Patsch91/NerdOCTAXE-Plus/BM1368-1.kicad_sch

## KiCad design BM1368-1.kicad_sch (2024-08-18)

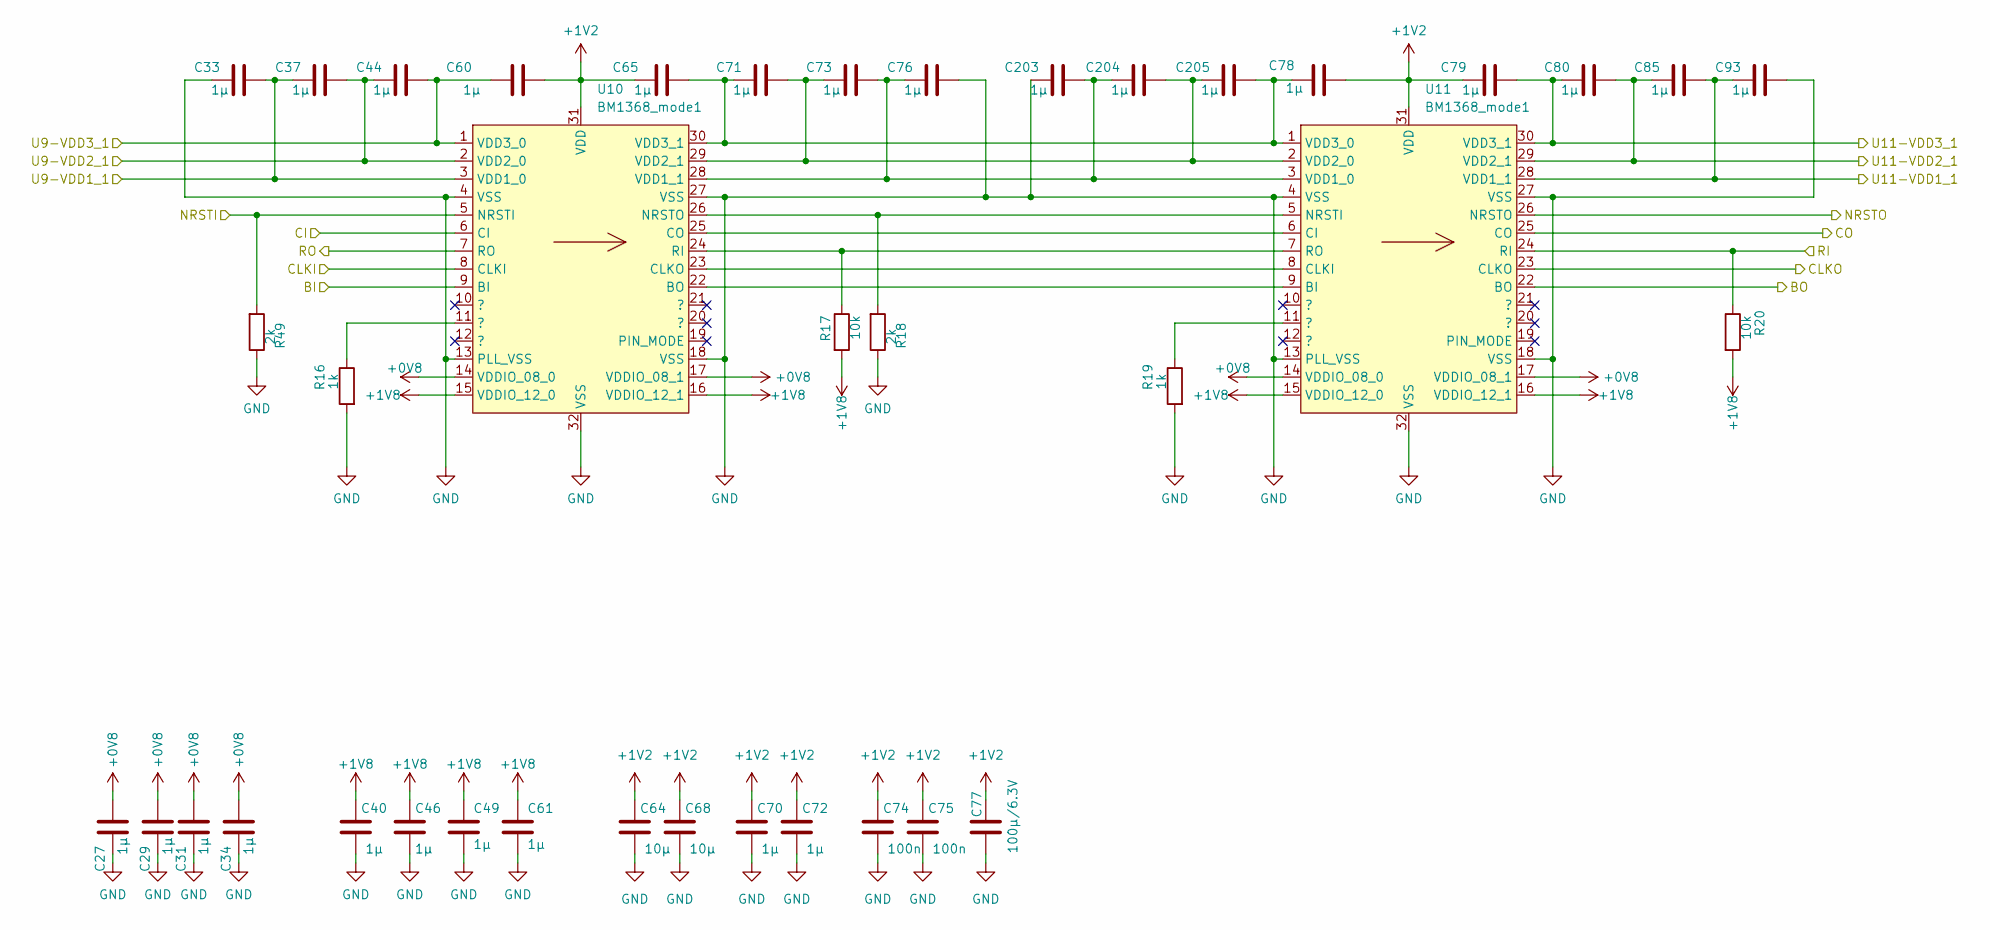
[picture p11: schematic BM1368-1.kicad_sch]

Parts:
C27, C29, C31, C33, C34, C37, C40, C44, C46, C49, C60, C61, C65, C70, C71, C72, C73, C76, C78, C79, C80, C85, C93, C203, C204, C205: 1µ; C_0805_2012Metric
C64, C68: 10µ; C_0805_2012Metric
C74, C75: 100n; C_0805_2012Metric
C77: 100µ/6.3V; C_1210_3225Metric
R16, R19: 1k; R_0805_2012Metric
R17, R20: 10k; R_0805_2012Metric
R18, R49: 2k; R_0805_2012Metric
U10, U11: BM1368_mode1; bm1368-package-modified

Connections:
+0V8: C27.2, C29.2, C31.2, C34.2, U10.14 (VDDIO_08_0), U10.17 (VDDIO_08_1), U11.14 (VDDIO_08_0), U11.17 (VDDIO_08_1)
+1V2: C60.2, C64.1, C65.1, C68.1, C70.1, C72.1, C74.1, C75.1, C77.1, C78.2, C79.1, U10.31 (VDD), U11.31 (VDD)
+1V8: C40.1, C46.1, C49.1, C61.1, R17.2, R20.2, U10.15 (VDDIO_12_0), U10.16 (VDDIO_12_1), U11.15 (VDDIO_12_0), U11.16 (VDDIO_12_1)
BI: U10.9 (BI)
BO: U11.22 (BO)
CI: U10.6 (CI)
CLKI: U10.8 (CLKI)
CLKO: U11.23 (CLKO)
CO: U11.25 (CO)
GND: C27.1, C29.1, C31.1, C33.1, C34.1, C40.2, C46.2, C49.2, C61.2, C64.2, C68.2, C70.2, C72.2, C74.2, C75.2, C76.2, C77.2, C93.2, C203.1, R16.2, R18.1, R19.2, R49.1, U10.4 (VSS), U10.13 (PLL_VSS), U10.18 (VSS), U10.27 (VSS), U10.32 (VSS), U11.4 (VSS), U11.13 (PLL_VSS), U11.18 (VSS), U11.27 (VSS), U11.32 (VSS)
NRSTI: R49.2, U10.5 (NRSTI)
NRSTO: U11.26 (NRSTO)
unnamed: C73.2, C76.1, C203.2, C204.1, U10.28 (VDD1_1), U11.3 (VDD1_0)
unnamed: C71.2, C73.1, C204.2, C205.1, U10.29 (VDD2_1), U11.2 (VDD2_0)
unnamed: C65.2, C71.1, C78.1, C205.2, U10.30 (VDD3_1), U11.1 (VDD3_0)
unnamed: R16.1, U10.11 (?)
unnamed: R17.1, U10.24 (RI), U11.7 (RO)
unnamed: R18.2, U10.26 (NRSTO), U11.5 (NRSTI)
unnamed: R19.1, U11.11 (?)
unnamed: U10.22 (BO), U11.9 (BI)
unnamed: U10.23 (CLKO), U11.8 (CLKI)
unnamed: U10.25 (CO), U11.6 (CI)
RI: R20.1, U11.24 (RI)
RO: U10.7 (RO)
U9-VDD1_1: C33.2, C37.1, U10.3 (VDD1_0)
U9-VDD2_1: C37.2, C44.1, U10.2 (VDD2_0)
U9-VDD3_1: C44.2, C60.1, U10.1 (VDD3_0)
U11-VDD1_1: C85.2, C93.1, U11.28 (VDD1_1)
U11-VDD2_1: C80.2, C85.1, U11.29 (VDD2_1)
U11-VDD3_1: C79.2, C80.1, U11.30 (VDD3_1)
