Patsch91/NerdOCTAXE-Plus/BM1368-2.kicad_sch

## KiCad design BM1368-2.kicad_sch (2024-08-18)

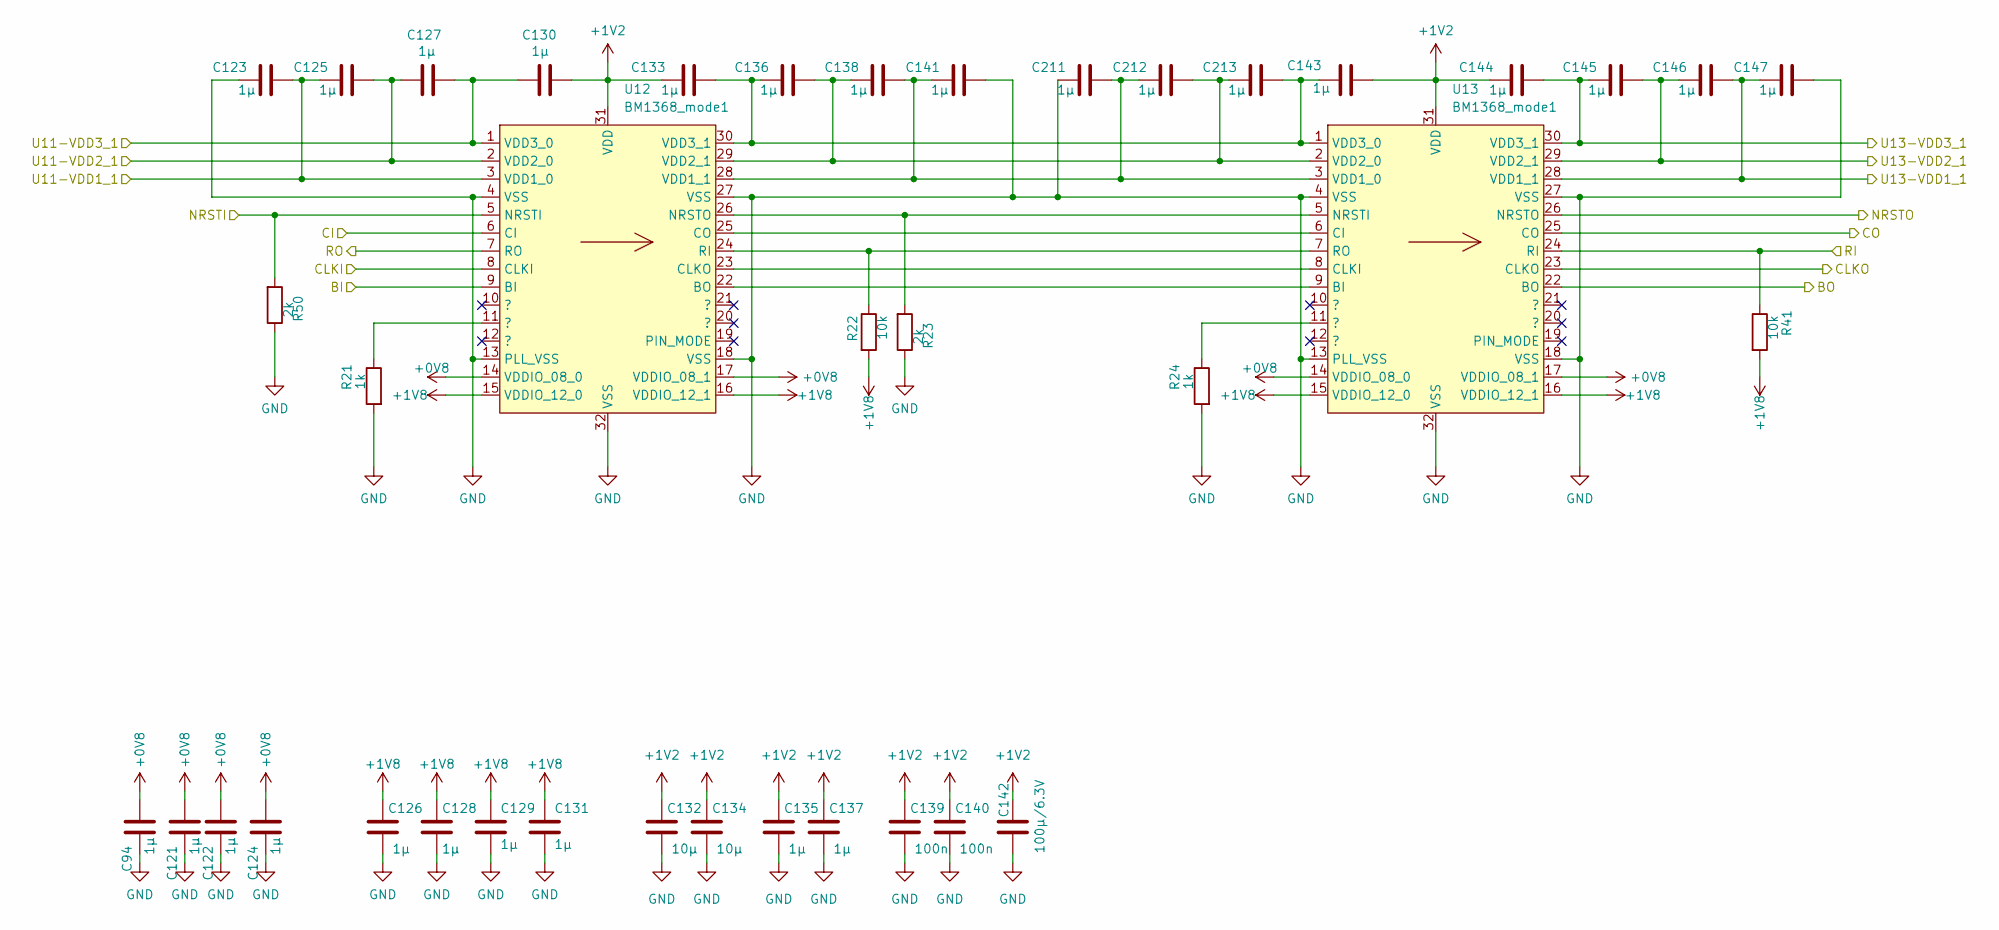
[picture p12: schematic BM1368-2.kicad_sch]

Parts:
C94, C121, C122, C123, C124, C125, C126, C127, C128, C129, C130, C131, C133, C135, C136, C137, C138, C141, C143, C144, C145, C146, C147, C211, C212, C213: 1µ; C_0805_2012Metric
C132, C134: 10µ; C_0805_2012Metric
C139, C140: 100n; C_0805_2012Metric
C142: 100µ/6.3V; C_1210_3225Metric
R21, R24: 1k; R_0805_2012Metric
R22, R41: 10k; R_0805_2012Metric
R23, R50: 2k; R_0805_2012Metric
U12, U13: BM1368_mode1; bm1368-package-modified

Connections:
+0V8: C94.2, C121.2, C122.2, C124.2, U12.14 (VDDIO_08_0), U12.17 (VDDIO_08_1), U13.14 (VDDIO_08_0), U13.17 (VDDIO_08_1)
+1V2: C130.2, C132.1, C133.1, C134.1, C135.1, C137.1, C139.1, C140.1, C142.1, C143.2, C144.1, U12.31 (VDD), U13.31 (VDD)
+1V8: C126.1, C128.1, C129.1, C131.1, R22.2, R41.2, U12.15 (VDDIO_12_0), U12.16 (VDDIO_12_1), U13.15 (VDDIO_12_0), U13.16 (VDDIO_12_1)
BI: U12.9 (BI)
BO: U13.22 (BO)
CI: U12.6 (CI)
CLKI: U12.8 (CLKI)
CLKO: U13.23 (CLKO)
CO: U13.25 (CO)
GND: C94.1, C121.1, C122.1, C123.1, C124.1, C126.2, C128.2, C129.2, C131.2, C132.2, C134.2, C135.2, C137.2, C139.2, C140.2, C141.2, C142.2, C147.2, C211.1, R21.2, R23.1, R24.2, R50.1, U12.4 (VSS), U12.13 (PLL_VSS), U12.18 (VSS), U12.27 (VSS), U12.32 (VSS), U13.4 (VSS), U13.13 (PLL_VSS), U13.18 (VSS), U13.27 (VSS), U13.32 (VSS)
NRSTI: R50.2, U12.5 (NRSTI)
NRSTO: U13.26 (NRSTO)
unnamed: C133.2, C136.1, C143.1, C213.2, U12.30 (VDD3_1), U13.1 (VDD3_0)
unnamed: C136.2, C138.1, C212.2, C213.1, U12.29 (VDD2_1), U13.2 (VDD2_0)
unnamed: C138.2, C141.1, C211.2, C212.1, U12.28 (VDD1_1), U13.3 (VDD1_0)
unnamed: R21.1, U12.11 (?)
unnamed: R22.1, U12.24 (RI), U13.7 (RO)
unnamed: R23.2, U12.26 (NRSTO), U13.5 (NRSTI)
unnamed: R24.1, U13.11 (?)
unnamed: U12.22 (BO), U13.9 (BI)
unnamed: U12.23 (CLKO), U13.8 (CLKI)
unnamed: U12.25 (CO), U13.6 (CI)
RI: R41.1, U13.24 (RI)
RO: U12.7 (RO)
U11-VDD1_1: C123.2, C125.1, U12.3 (VDD1_0)
U11-VDD2_1: C125.2, C127.1, U12.2 (VDD2_0)
U11-VDD3_1: C127.2, C130.1, U12.1 (VDD3_0)
U13-VDD1_1: C146.2, C147.1, U13.28 (VDD1_1)
U13-VDD2_1: C145.2, C146.1, U13.29 (VDD2_1)
U13-VDD3_1: C144.2, C145.1, U13.30 (VDD3_1)
