Patsch91/NerdOCTAXE-Plus/BM1368-3.kicad_sch

## KiCad design BM1368-3.kicad_sch (2024-08-18)

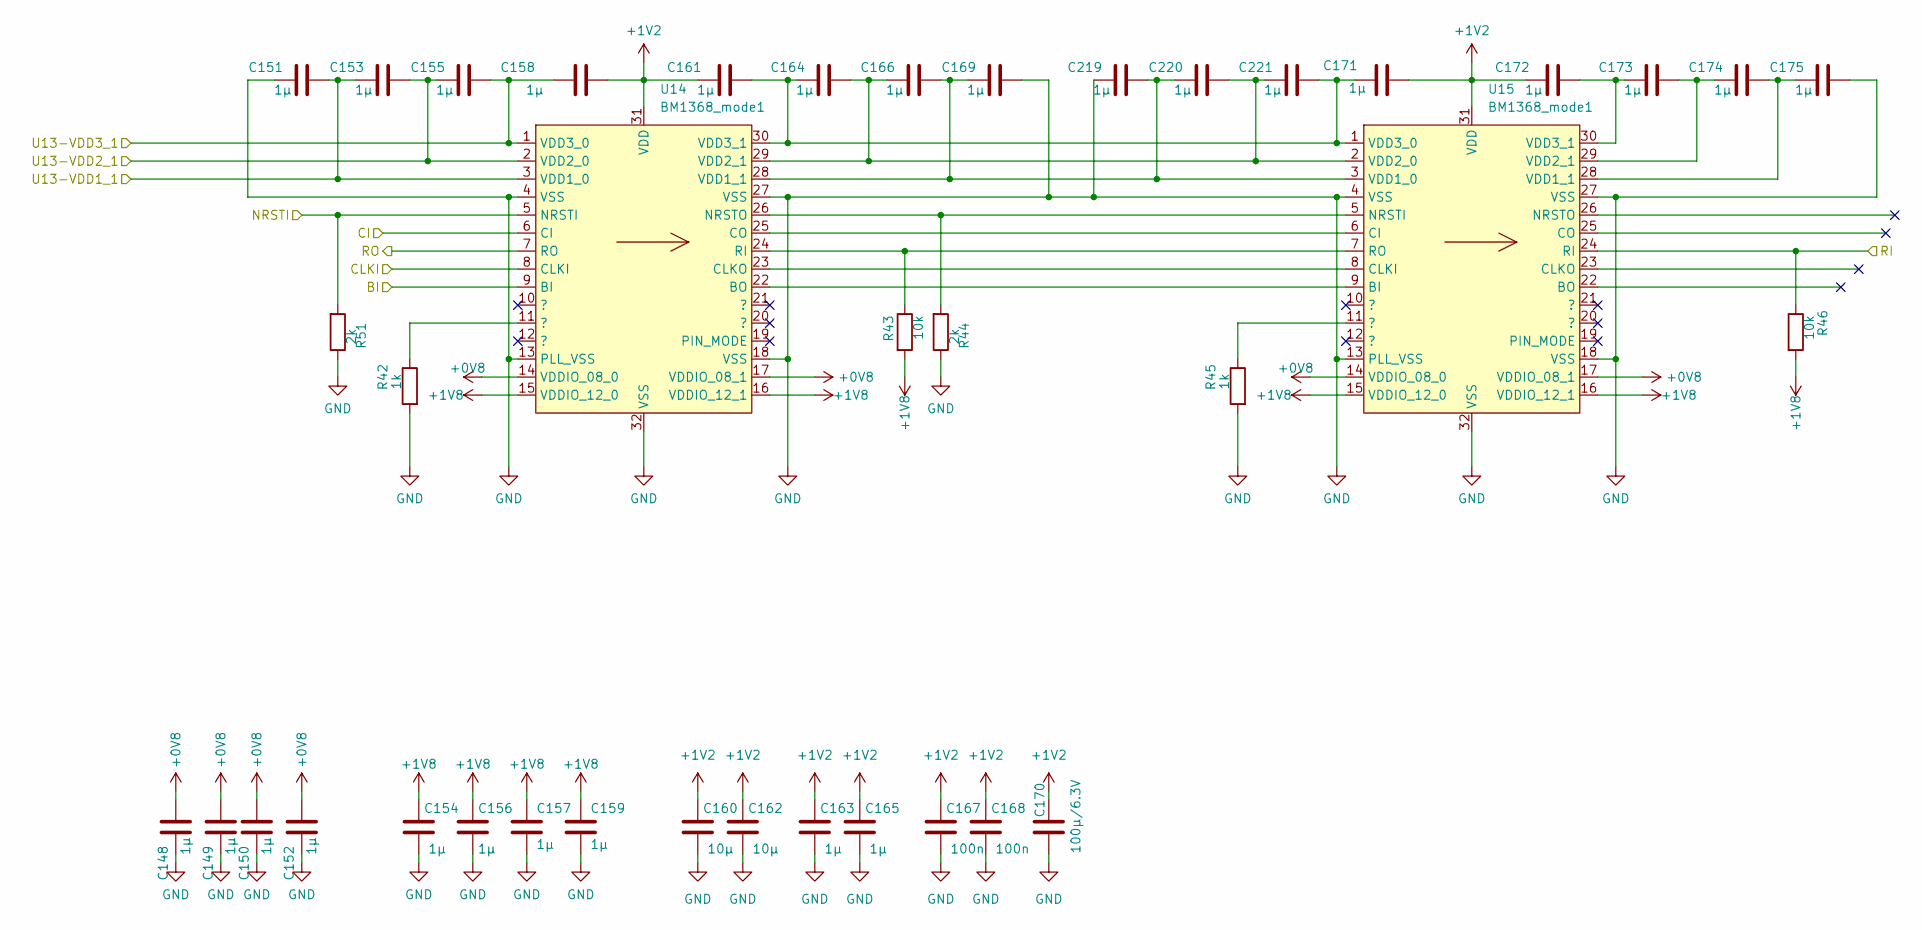
[picture p13: schematic BM1368-3.kicad_sch]

Parts:
C148, C149, C150, C151, C152, C153, C154, C155, C156, C157, C158, C159, C161, C163, C164, C165, C166, C169, C171, C172, C173, C174, C175, C219, C220, C221: 1µ; C_0805_2012Metric
C160, C162: 10µ; C_0805_2012Metric
C167, C168: 100n; C_0805_2012Metric
C170: 100µ/6.3V; C_1210_3225Metric
R42, R45: 1k; R_0805_2012Metric
R43, R46: 10k; R_0805_2012Metric
R44, R51: 2k; R_0805_2012Metric
U14, U15: BM1368_mode1; bm1368-package-modified

Connections:
+0V8: C148.2, C149.2, C150.2, C152.2, U14.14 (VDDIO_08_0), U14.17 (VDDIO_08_1), U15.14 (VDDIO_08_0), U15.17 (VDDIO_08_1)
+1V2: C158.2, C160.1, C161.1, C162.1, C163.1, C165.1, C167.1, C168.1, C170.1, C171.2, C172.1, U14.31 (VDD), U15.31 (VDD)
+1V8: C154.1, C156.1, C157.1, C159.1, R43.2, R46.2, U14.15 (VDDIO_12_0), U14.16 (VDDIO_12_1), U15.15 (VDDIO_12_0), U15.16 (VDDIO_12_1)
BI: U14.9 (BI)
CI: U14.6 (CI)
CLKI: U14.8 (CLKI)
GND: C148.1, C149.1, C150.1, C151.1, C152.1, C154.2, C156.2, C157.2, C159.2, C160.2, C162.2, C163.2, C165.2, C167.2, C168.2, C169.2, C170.2, C175.2, C219.1, R42.2, R44.1, R45.2, R51.1, U14.4 (VSS), U14.13 (PLL_VSS), U14.18 (VSS), U14.27 (VSS), U14.32 (VSS), U15.4 (VSS), U15.13 (PLL_VSS), U15.18 (VSS), U15.27 (VSS), U15.32 (VSS)
NRSTI: R51.2, U14.5 (NRSTI)
unnamed: C161.2, C164.1, C171.1, C221.2, U14.30 (VDD3_1), U15.1 (VDD3_0)
unnamed: C164.2, C166.1, C220.2, C221.1, U14.29 (VDD2_1), U15.2 (VDD2_0)
unnamed: C166.2, C169.1, C219.2, C220.1, U14.28 (VDD1_1), U15.3 (VDD1_0)
unnamed: C172.2, C173.1, U15.30 (VDD3_1)
unnamed: C173.2, C174.1, U15.29 (VDD2_1)
unnamed: C174.2, C175.1, U15.28 (VDD1_1)
unnamed: R42.1, U14.11 (?)
unnamed: R43.1, U14.24 (RI), U15.7 (RO)
unnamed: R44.2, U14.26 (NRSTO), U15.5 (NRSTI)
unnamed: R45.1, U15.11 (?)
unnamed: U14.22 (BO), U15.9 (BI)
unnamed: U14.23 (CLKO), U15.8 (CLKI)
unnamed: U14.25 (CO), U15.6 (CI)
RI: R46.1, U15.24 (RI)
RO: U14.7 (RO)
U13-VDD1_1: C151.2, C153.1, U14.3 (VDD1_0)
U13-VDD2_1: C153.2, C155.1, U14.2 (VDD2_0)
U13-VDD3_1: C155.2, C158.1, U14.1 (VDD3_0)
