Patsch91/NerdOCTAXE-Plus/BM1368.kicad_sch

## KiCad design BM1368.kicad_sch (2024-08-18)

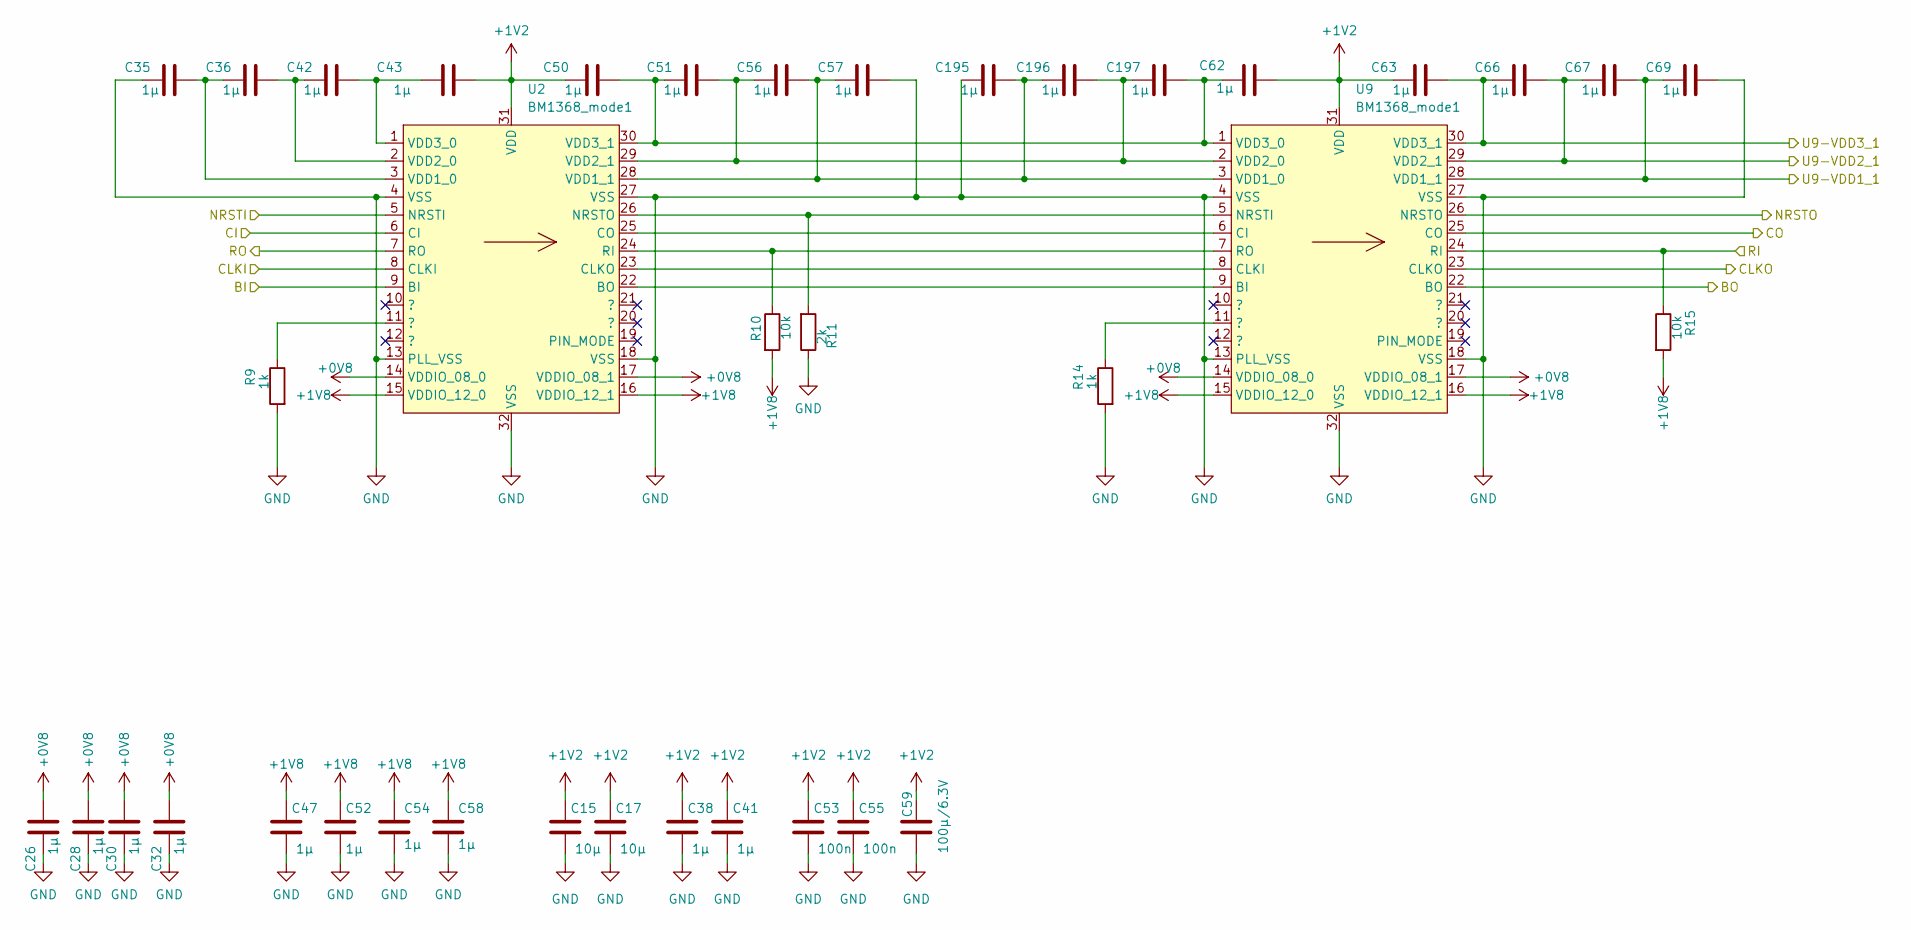
[picture p14: schematic BM1368.kicad_sch]

Parts:
C15, C17: 10µ; C_0805_2012Metric
C26, C28, C30, C32, C35, C36, C38, C41, C42, C43, C47, C50, C51, C52, C54, C56, C57, C58, C62, C63, C66, C67, C69, C195, C196, C197: 1µ; C_0805_2012Metric
C53, C55: 100n; C_0805_2012Metric
C59: 100µ/6.3V; C_1210_3225Metric
R9, R14: 1k; R_0805_2012Metric
R10, R15: 10k; R_0805_2012Metric
R11: 2k; R_0805_2012Metric
U2, U9: BM1368_mode1; bm1368-package-modified

Connections:
+0V8: C26.2, C28.2, C30.2, C32.2, U2.14 (VDDIO_08_0), U2.17 (VDDIO_08_1), U9.14 (VDDIO_08_0), U9.17 (VDDIO_08_1)
+1V2: C15.1, C17.1, C38.1, C41.1, C43.2, C50.1, C53.1, C55.1, C59.1, C62.2, C63.1, U2.31 (VDD), U9.31 (VDD)
+1V8: C47.1, C52.1, C54.1, C58.1, R10.2, R15.2, U2.15 (VDDIO_12_0), U2.16 (VDDIO_12_1), U9.15 (VDDIO_12_0), U9.16 (VDDIO_12_1)
BI: U2.9 (BI)
BO: U9.22 (BO)
CI: U2.6 (CI)
CLKI: U2.8 (CLKI)
CLKO: U9.23 (CLKO)
CO: U9.25 (CO)
GND: C15.2, C17.2, C26.1, C28.1, C30.1, C32.1, C35.1, C38.2, C41.2, C47.2, C52.2, C53.2, C54.2, C55.2, C57.2, C58.2, C59.2, C69.2, C195.1, R9.2, R11.1, R14.2, U2.4 (VSS), U2.13 (PLL_VSS), U2.18 (VSS), U2.27 (VSS), U2.32 (VSS), U9.4 (VSS), U9.13 (PLL_VSS), U9.18 (VSS), U9.27 (VSS), U9.32 (VSS)
NRSTI: U2.5 (NRSTI)
NRSTO: U9.26 (NRSTO)
unnamed: C35.2, C36.1, U2.3 (VDD1_0)
unnamed: C36.2, C42.1, U2.2 (VDD2_0)
unnamed: C42.2, C43.1, U2.1 (VDD3_0)
unnamed: C56.2, C57.1, C195.2, C196.1, U2.28 (VDD1_1), U9.3 (VDD1_0)
unnamed: C51.2, C56.1, C196.2, C197.1, U2.29 (VDD2_1), U9.2 (VDD2_0)
unnamed: C50.2, C51.1, C62.1, C197.2, U2.30 (VDD3_1), U9.1 (VDD3_0)
unnamed: R9.1, U2.11 (?)
unnamed: R10.1, U2.24 (RI), U9.7 (RO)
unnamed: R11.2, U2.26 (NRSTO), U9.5 (NRSTI)
unnamed: R14.1, U9.11 (?)
unnamed: U2.22 (BO), U9.9 (BI)
unnamed: U2.23 (CLKO), U9.8 (CLKI)
unnamed: U2.25 (CO), U9.6 (CI)
RI: R15.1, U9.24 (RI)
RO: U2.7 (RO)
U9-VDD1_1: C67.2, C69.1, U9.28 (VDD1_1)
U9-VDD2_1: C66.2, C67.1, U9.29 (VDD2_1)
U9-VDD3_1: C63.2, C66.1, U9.30 (VDD3_1)
