Patsch91/NerdOCTAXE-Plus/Nerd8.kicad_sch

## KiCad design Nerd8.kicad_sch (2024-09-09)

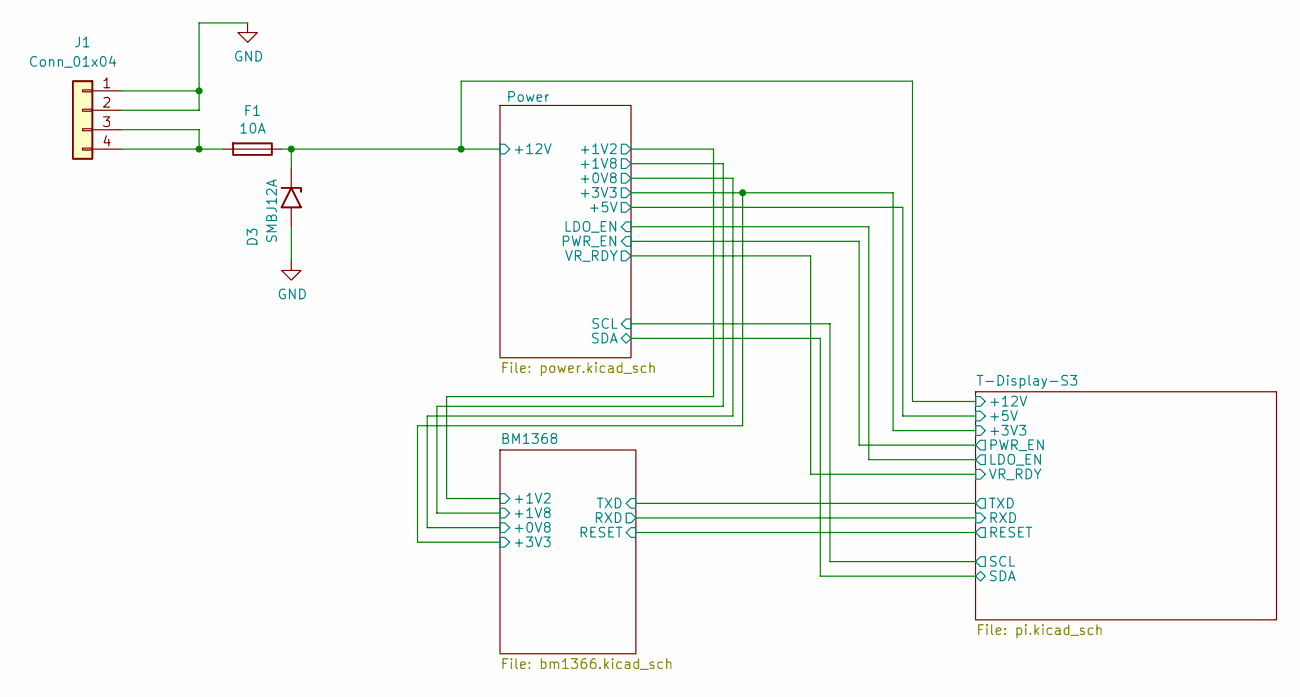
[picture p15: schematic Nerd8.kicad_sch]

Parts:
D3: SMBJ12A; D_SMB
F1: 10A; fuseholder_littlefuse_blok
J1: Conn_01x04; Barrier Terminal 01x04

Connections:
+12V: D3.1 (A1), F1.1
GND: D3.2 (A2), J1.1, J1.2
unnamed: F1.2, J1.3, J1.4
