Patsch91/NerdOCTAXE-Plus/bm1366.kicad_sch

## KiCad design bm1366.kicad_sch (2024-08-18)

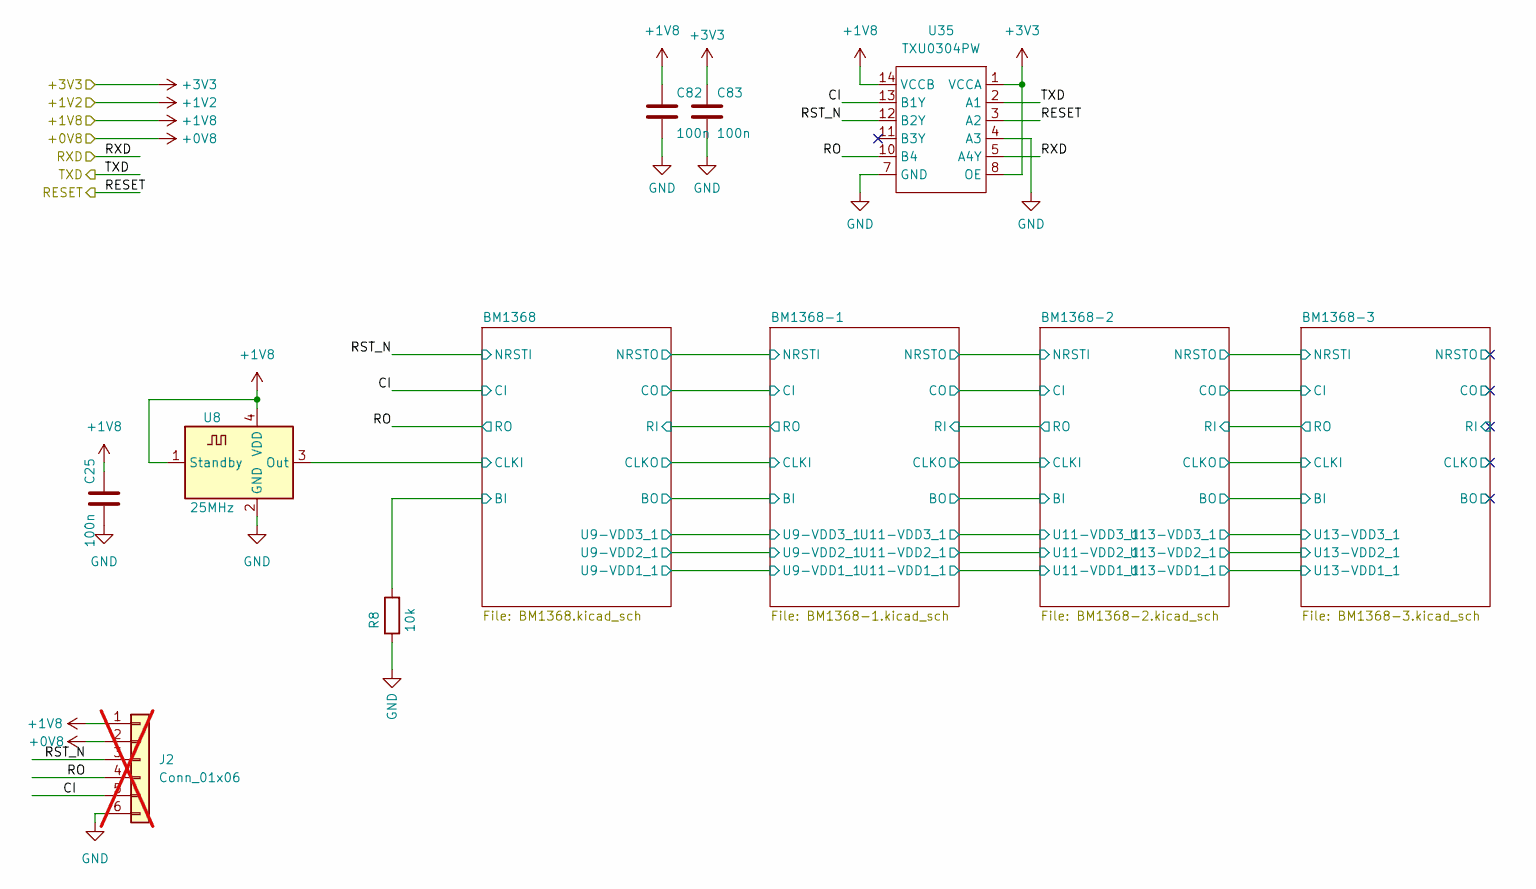
[picture p16: schematic bm1366.kicad_sch]

Parts:
C25, C82, C83: 100n; C_0805_2012Metric
J2: Conn_01x06; PinHeader_1x06_P1.27mm_Vertical; not fitted
R8: 10k; R_0805_2012Metric
U8: 25MHz; Oscillator_SMD_EuroQuartz_XO32-4Pin_3.2x2.5mm
U35: TXU0304PW; TSSOP-14-1EP_4.4x5mm_P0.65mm

Connections:
+0V8: J2.2
+1V8: C25.1, C82.1, J2.1, U8.1 (Standby), U8.4 (VDD), U35.14 (VCCB)
+3V3: C83.1, U35.1 (VCCA), U35.8 (OE)
BI: R8.2
CI: J2.5, U35.13 (B1Y)
CLKI: U8.3 (Out)
GND: C25.2, C82.2, C83.2, J2.6, R8.1, U8.2 (GND), U35.4 (A3), U35.7 (GND)
RESET: U35.3 (A2)
RO: J2.4, U35.10 (B4)
RST_N: J2.3, U35.12 (B2Y)
RXD: U35.5 (A4Y)
TXD: U35.2 (A1)
