Patsch91/NerdOCTAXE-Plus/pi.kicad_sch

## KiCad design pi.kicad_sch (2024-08-14)

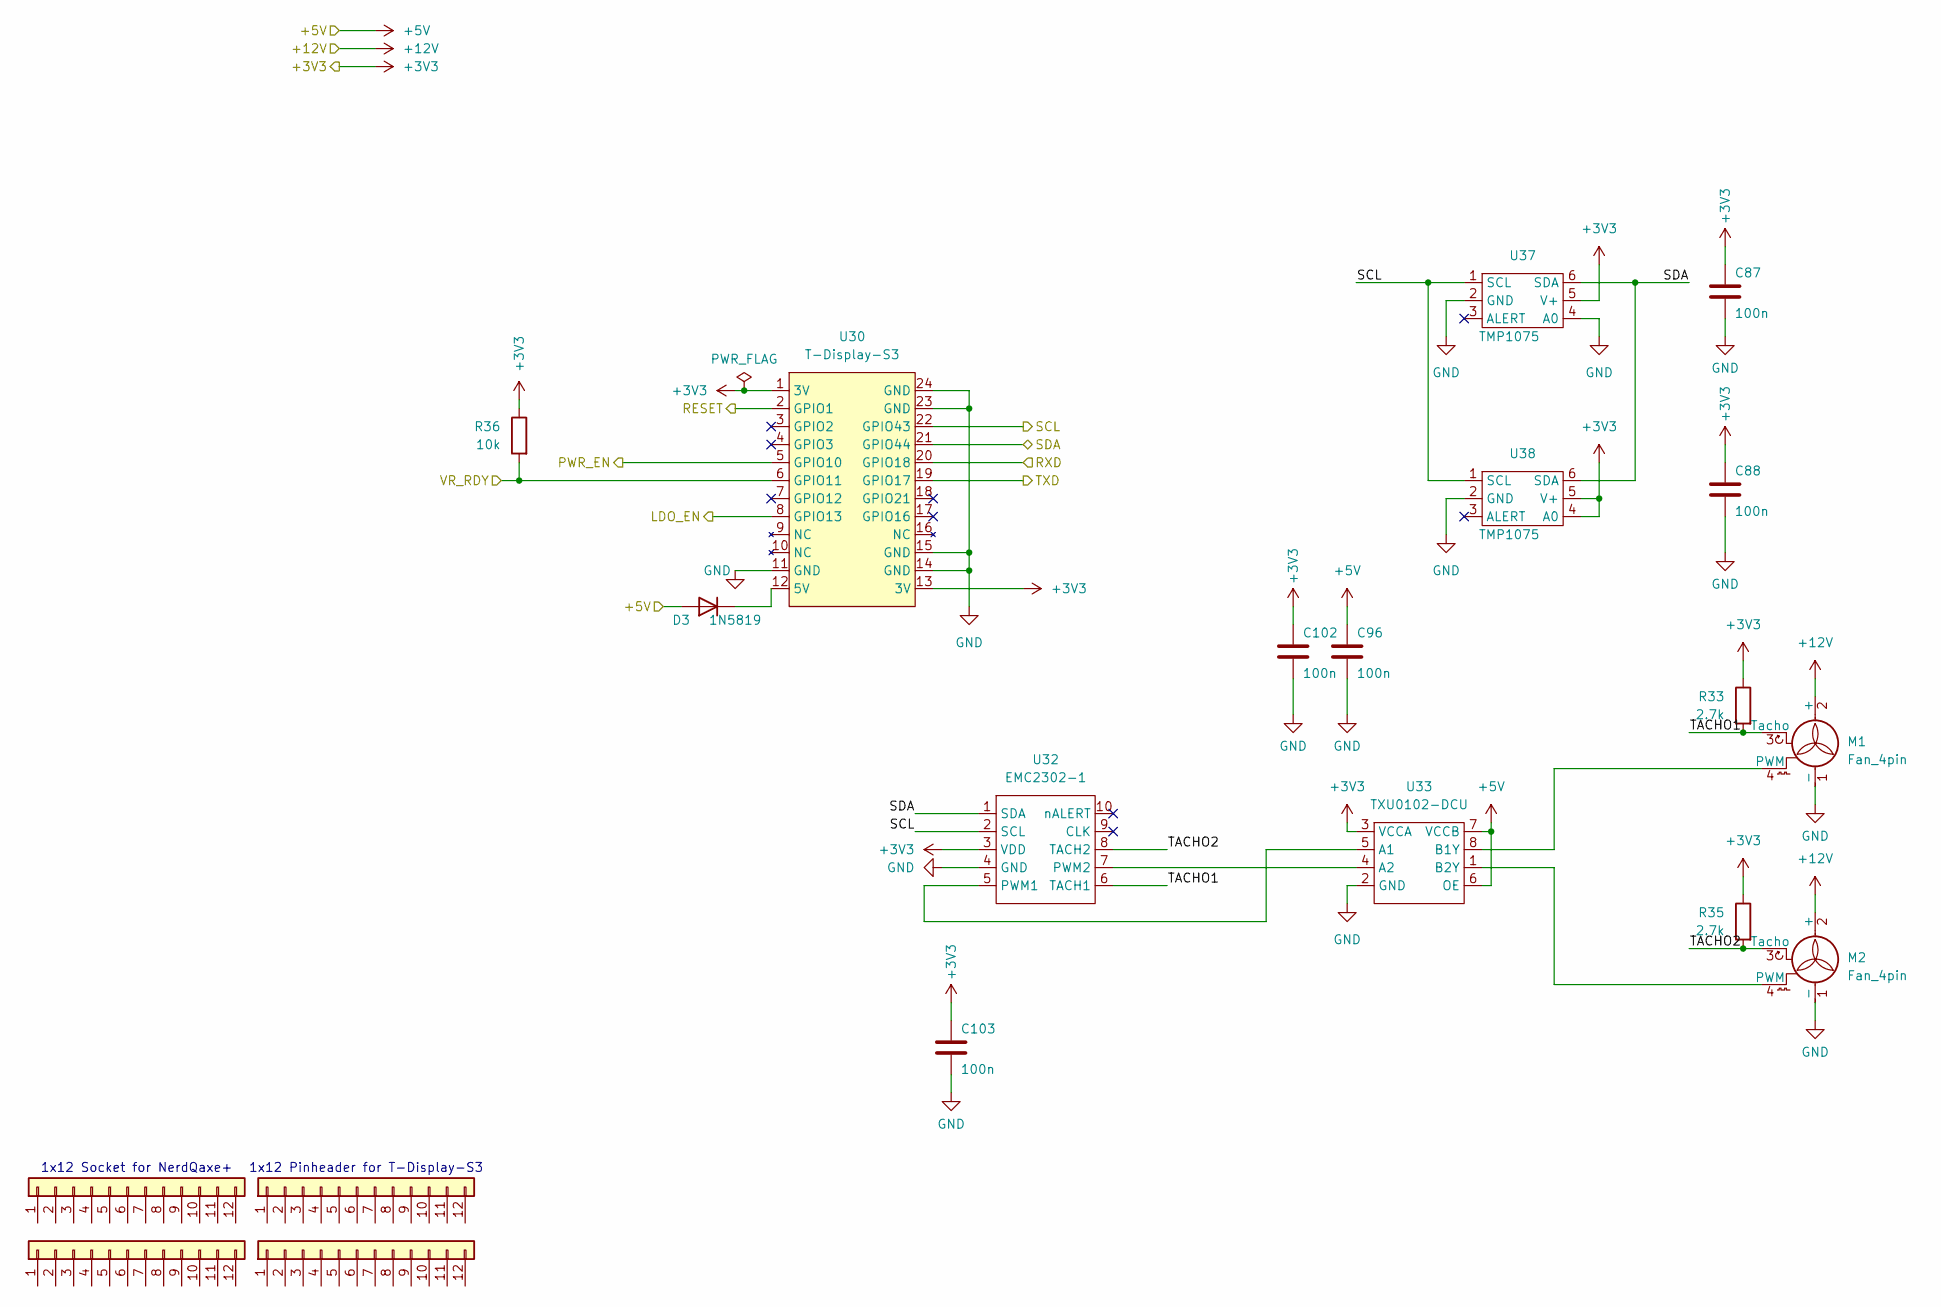
[picture p17: schematic pi.kicad_sch]

Parts:
C87, C88, C96, C102, C103: 100n; C_0805_2012Metric
D3: 1N5819; D_SOD-123
J5, J6: Conn_01x12-Socket
J7, J8: Conn_01x12-Header
M1, M2: Fan_4pin; FanPinHeader_1x04_P2.54mm_Vertical
R33, R35: 2.7k; R_0805_2012Metric
R36: 10k; R_0805_2012Metric
U30: T-Display-S3
U32: EMC2302-1; MSOP-10_3x3mm_P0.5mm
U33: TXU0102-DCU; VSSOP-8_2.3x2mm_P0.5mm
U37, U38: TMP1075; TMP1075-DRL

Connections:
+3V3: C87.1, C88.1, C102.1, C103.1, R33.1, R35.1, R36.1, U30.1 (3V), U30.13 (3V), U32.3 (VDD), U33.3 (VCCA), U37.5 (V+), U38.4 (A0), U38.5 (V+)
+5V: C96.1, D3.2 (A), U33.6 (OE), U33.7 (VCCB)
+12V: M1.2 (+), M2.2 (+)
GND: C87.2, C88.2, C96.2, C102.2, C103.2, M1.1 (-), M2.1 (-), U30.11 (GND), U30.14 (GND), U30.15 (GND), U30.23 (GND), U30.24 (GND), U32.4 (GND), U33.2 (GND), U37.2 (GND), U37.4 (A0), U38.2 (GND)
LDO_EN: U30.8 (GPIO13)
unnamed: D3.1 (K), U30.12 (5V)
unnamed: M1.4 (PWM), U33.8 (B1Y)
unnamed: M2.4 (PWM), U33.1 (B2Y)
unnamed: U32.5 (PWM1), U33.5 (A1)
unnamed: U32.7 (PWM2), U33.4 (A2)
PWR_EN: U30.5 (GPIO10)
RESET: U30.2 (GPIO1)
RXD: U30.20 (GPIO18)
SCL: U30.22 (GPIO43), U32.2 (SCL), U37.1 (SCL), U38.1 (SCL)
SDA: U30.21 (GPIO44), U32.1 (SDA), U37.6 (SDA), U38.6 (SDA)
TACHO1: M1.3 (Tacho), R33.2, U32.6 (TACH1)
TACHO2: M2.3 (Tacho), R35.2, U32.8 (TACH2)
TXD: U30.19 (GPIO17)
VR_RDY: R36.2, U30.6 (GPIO11)

Notes on the sheet:
1x12 Socket for NerdQaxe+
1x12 Pinheader for T-Display-S3
