Patsch91/NerdOCTAXE-Plus/power.kicad_sch

## KiCad design power.kicad_sch (2024-09-18)

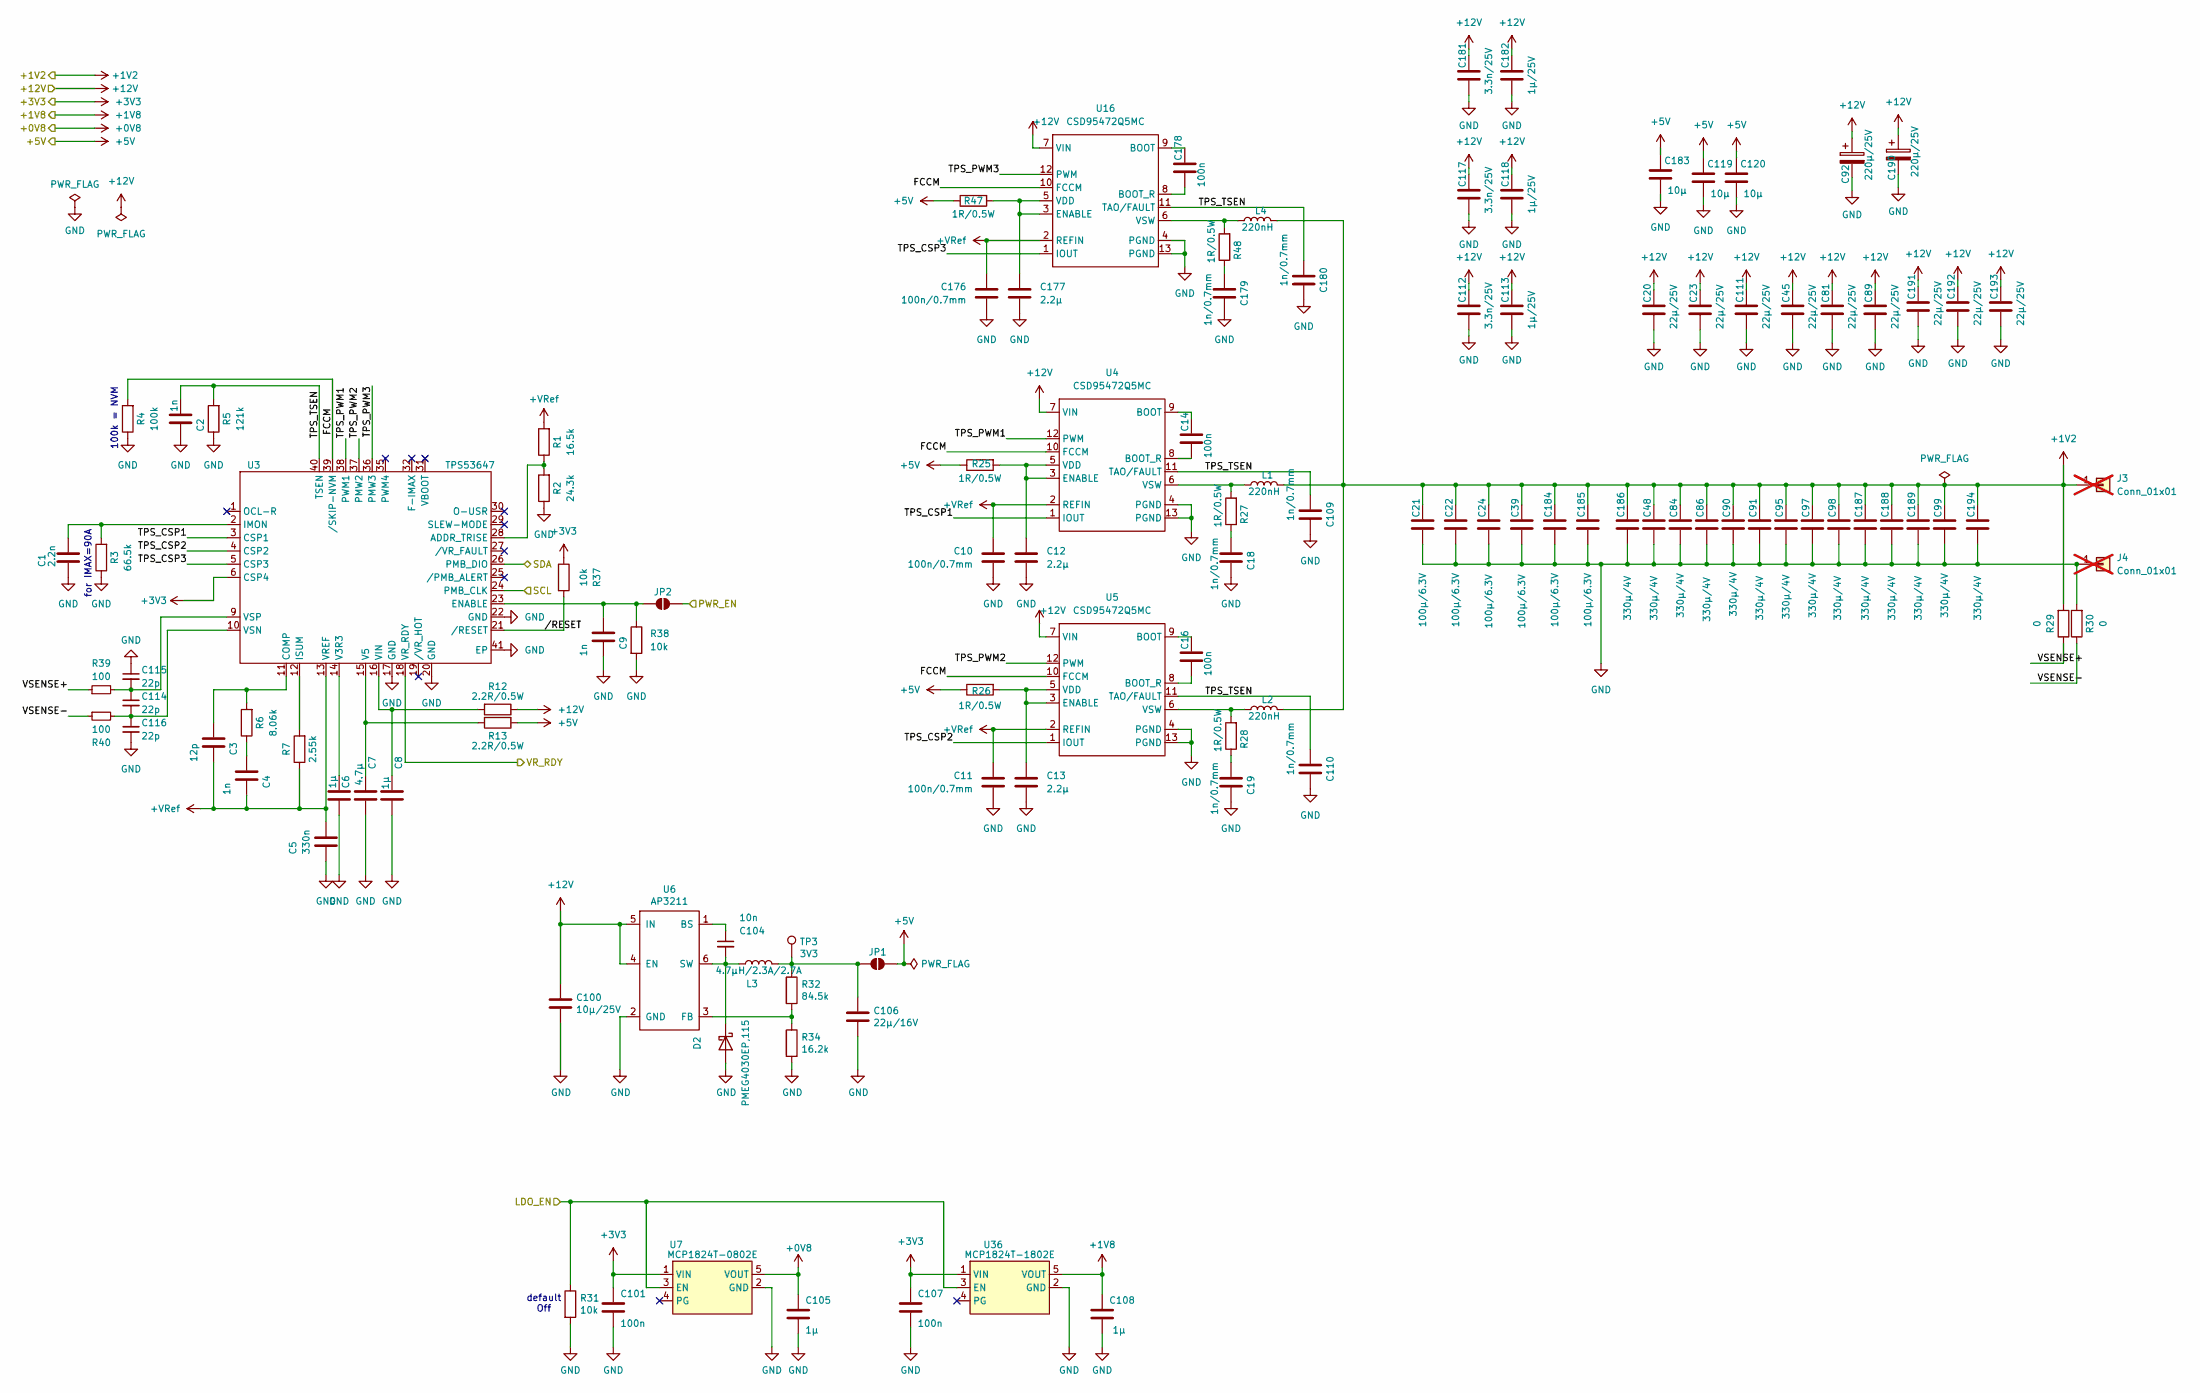
[picture p18: schematic power.kicad_sch]

Parts:
C1: 2.2n; C_0805_2012Metric
C2, C4, C9: 1n; C_0805_2012Metric
C3: 12p; C_0603_1608Metric
C5: 330n; C_0805_2012Metric
C6, C8, C105, C108: 1µ; C_0805_2012Metric
C7: 4.7µ; C_0805_2012Metric
C10, C11, C176: 100n/0.7mm; C_0805_2012Metric
C12, C13, C177: 2.2µ; C_0805_2012Metric
C14, C16, C101, C107, C178: 100n; C_0805_2012Metric
C18, C19, C109, C110, C179, C180: 1n/0.7mm; C_0805_2012Metric
C20, C23, C45, C81, C89, C111, C191, C192, C193: 22µ/25V; C_1210_3225Metric
C21, C22, C24, C39, C184, C185: 100µ/6.3V; C_1210_3225Metric
C48, C84, C86, C90, C91, C95, C97, C98, C99, C186, C187, C188, C189, C194: 330µ/4V; C_1210_3225Metric
C92, C190: 220µ/25V; CP_Elec_8x10
C100: 10µ/25V; C_0805_2012Metric
C104: 10n; C_0805_2012Metric
C106: 22µ/16V; C_1206_3216Metric
C112, C117, C181: 3.3n/25V; C_0805_2012Metric
C113, C118, C182: 1µ/25V; C_0805_2012Metric
C114, C115, C116: 22p; C_0603_1608Metric
C119, C120, C183: 10µ; C_0805_2012Metric
D2: PMEG4030EP,115; D_SOD-128
J3, J4: Conn_01x01; Wuerth_REDCUBE-THR_WP-THRBU_74650194_THR; not fitted
JP1, JP2: SolderJumper_2_Open; SolderJumper-2_P1.3mm_Open_RoundedPad1.0x1.5mm
L1, L2, L4: 220nH; IFLR-4031GC-01-8x10
L3: 4.7µH/2.3A/2.7A; L_Taiyo-Yuden_NR-50xx
R1: 16.5k; R_0805_2012Metric
R2: 24.3k; R_0805_2012Metric
R3: 66.5k; R_0805_2012Metric
R4: 100k; R_0805_2012Metric
R5: 121k; R_0805_2012Metric
R6: 8.06k; R_0805_2012Metric
R7: 2.55k; R_0805_2012Metric
R12, R13: 2.2R/0.5W; R_0805_2012Metric
R25, R26, R27, R28, R47, R48: 1R/0.5W; R_0805_2012Metric
R29, R30: 0; R_0805_2012Metric
R31, R37, R38: 10k; R_0805_2012Metric
R32: 84.5k; R_0805_2012Metric
R34: 16.2k; R_0805_2012Metric
R39, R40: 100; R_0805_2012Metric
TP3: 3V3; TestPoint_Pad_2.0x2.0mm
U3: TPS53647; Texas_RHA0040B_VQFN-40-1EP_6x6mm_P0.5mm_EP4.15x4.15mm_Therm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
U4, U5, U16: CSD95472Q5MC; CSD95472-SON-5x6
U6: AP3211; SOT-23-6
U7: MCP1824T-0802E; SOT-23-5
U36: MCP1824T-1802E; SOT-23-5

Connections:
+0V8: C105.1, U7.5 (VOUT)
+1V2: C21.1, C22.1, C24.1, C39.1, C48.1, C84.1, C86.1, C90.1, C91.1, C95.1, C97.1, C98.1, C99.1, C184.1, C185.1, C186.1, C187.1, C188.1, C189.1, C194.1, J3.1, L1.2, L2.2, L4.2, R29.2
+1V8: C108.1, U36.5 (VOUT)
+3V3: C101.1, C107.1, R37.1, U3.6 (CSP4), U7.1 (VIN), U36.1 (VIN)
+5V: C119.1, C120.1, C183.1, JP1.2 (B), R13.1, R25.1, R26.1, R47.1
+12V: C20.1, C23.1, C45.1, C81.1, C89.1, C92.1, C100.1, C111.1, C112.1, C113.1, C117.1, C118.1, C181.1, C182.1, C190.1, C191.1, C192.1, C193.1, R12.1, U4.7 (VIN), U5.7 (VIN), U6.4 (EN), U6.5 (IN), U16.7 (VIN)
+VRef: C3.2, C4.2, C5.1, C10.1, C11.1, C176.1, R1.2, R7.1, U3.13 (VREF), U4.2 (REFIN), U5.2 (REFIN), U16.2 (REFIN)
FCCM: R4.2, U3.39 (/SKIP-NVM), U4.10 (FCCM), U5.10 (FCCM), U16.10 (FCCM)
GND: C1.2, C2.2, C5.2, C6.2, C7.1, C8.1, C9.2, C10.2, C11.2, C12.2, C13.2, C18.2, C19.2, C20.2, C21.2, C22.2, C23.2, C24.2, C39.2, C45.2, C48.2, C81.2, C84.2, C86.2, C89.2, C90.2, C91.2, C92.2, C95.2, C97.2, C98.2, C99.2, C100.2, C101.2, C105.2, C106.2, C107.2, C108.2, C109.2, C110.2, C111.2, C112.2, C113.2, C115.1, C116.2, C117.2, C118.2, C119.2, C120.2, C176.2, C177.2, C179.2, C180.2, C181.2, C182.2, C183.2, C184.2, C185.2, C186.2, C187.2, C188.2, C189.2, C190.2, C191.2, C192.2, C193.2, C194.2, D2.2 (A), J4.1, R2.1, R3.1, R4.1, R5.1, R30.2, R31.2, R34.2, R38.2, U3.17 (GND), U3.20 (GND), U3.22 (GND), U3.41 (EP), U4.4 (PGND), U4.13 (PGND), U5.4 (PGND), U5.13 (PGND), U6.2 (GND), U7.2 (GND), U16.4 (PGND), U16.13 (PGND), U36.2 (GND)
LDO_EN: R31.1, U7.3 (EN), U36.3 (EN)
unnamed: C1.1, R3.2, U3.2 (IMON)
unnamed: C3.1, R6.2, U3.11 (COMP)
unnamed: C4.1, R6.1
unnamed: C6.1, U3.14 (V3R3)
unnamed: C7.2, R13.2, U3.15 (V5)
unnamed: C8.2, R12.2, U3.16 (VIN)
unnamed: C9.1, JP2.1 (A), R38.1, U3.23 (ENABLE)
unnamed: C12.1, R25.2, U4.3 (ENABLE), U4.5 (VDD)
unnamed: C13.1, R26.2, U5.3 (ENABLE), U5.5 (VDD)
unnamed: C14.1, U4.9 (BOOT)
unnamed: C14.2, U4.8 (BOOT_R)
unnamed: C16.1, U5.9 (BOOT)
unnamed: C16.2, U5.8 (BOOT_R)
unnamed: C18.1, R27.1
unnamed: C19.1, R28.1
unnamed: C104.1, U6.1 (BS)
unnamed: C104.2, D2.1 (K), L3.1, U6.6 (SW)
unnamed: C106.1, JP1.1 (A), L3.2, R32.1, TP3.1
unnamed: C114.1, C115.2, R39.2, U3.9 (VSP)
unnamed: C114.2, C116.1, R40.2, U3.10 (VSN)
unnamed: C177.1, R47.2, U16.3 (ENABLE), U16.5 (VDD)
unnamed: C178.1, U16.9 (BOOT)
unnamed: C178.2, U16.8 (BOOT_R)
unnamed: C179.1, R48.1
unnamed: L1.1, R27.2, U4.6 (VSW)
unnamed: L2.1, R28.2, U5.6 (VSW)
unnamed: L4.1, R48.2, U16.6 (VSW)
unnamed: R1.1, R2.2, U3.28 (ADDR_TRISE)
unnamed: R7.2, U3.12 (ISUM)
unnamed: R32.2, R34.1, U6.3 (FB)
PWR_EN: JP2.2 (B)
SCL: U3.24 (PMB_CLK)
SDA: U3.26 (PMB_DIO)
TPS_CSP1: U3.3 (CSP1), U4.1 (IOUT)
TPS_CSP2: U3.4 (CSP2), U5.1 (IOUT)
TPS_CSP3: U3.5 (CSP3), U16.1 (IOUT)
TPS_PWM1: U3.38 (PWM1), U4.12 (PWM)
TPS_PWM2: U3.37 (PMW2), U5.12 (PWM)
TPS_PWM3: U3.36 (PMW3), U16.12 (PWM)
TPS_TSEN: C2.1, C109.1, C110.1, C180.1, R5.2, U3.40 (TSEN), U4.11 (TAO/FAULT), U5.11 (TAO/FAULT), U16.11 (TAO/FAULT)
VR_RDY: U3.18 (VR_RDY)
VSENSE+: R29.1, R39.1
VSENSE-: R30.1, R40.1
/RESET: R37.2, U3.21 (/RESET)

Notes on the sheet:
default Off
for IMAX=90A
100k = NVM
